LeTo37/Ukulele_Player/Mechanical_Designs/Unused_Designs/Full_Assembly.stl

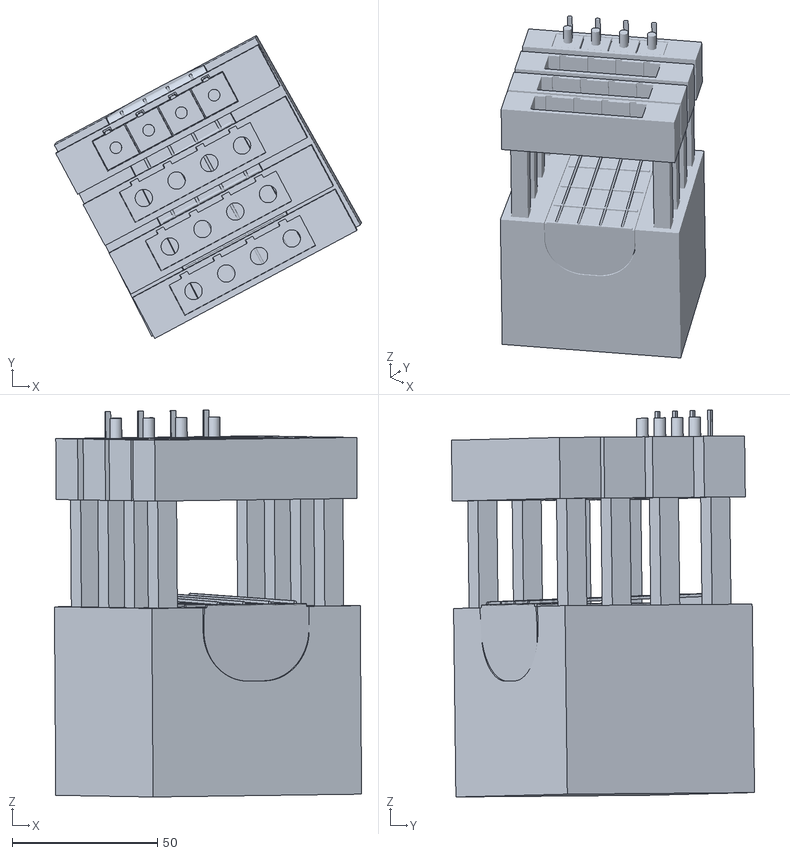
[picture p22: CAD file, 2019-02-07, an earlier design]
Mechanical_Designs/Unused_Designs/Full_Assembly.stl
105.9 x 104.5 x 133.4
