LeTo37/Ukulele_Player/Circuit_Schematics/LED.sch

## KiCad design Circuit_Schematics/LED.sch (2019-03-22)

Schematic: LED.sch

Parts:
D1: LED
D10: PIC32 Digital I/O
R1: 330
