LeTo37/Ukulele_Player/Circuit_Schematics/Solenoid_Drivers_1.sch

## KiCad design Circuit_Schematics/Solenoid_Drivers_1.sch (2019-03-22)

Schematic: Solenoid_Drivers_1.sch

Parts:
D1, D2, D3, D4, D5, D6, D7, D8: 1N4004
L1, L2, L3, L4, L5, L6, L7, L8: Solenoid
Q1, Q2, Q3, Q4, Q5, Q6, Q7, Q8: TIP120; TO-220_Vertical
R1, R2, R3, R4, R5, R6, R7, R8: 1k
RB0, RB1, RB2, RB3, RB4, RB5, RB6, RB7: PIC32 Digital I/O
