LeTo37/Ukulele_Player/Circuit_Schematics/Solenoid_Drivers_2.sch

## KiCad design Circuit_Schematics/Solenoid_Drivers_2.sch (2019-03-22)

Schematic: Solenoid_Drivers_2.sch

Parts:
D9, D10, D11, D12, D13, D14, D15, D16: 1N4004
L9, L10, L11, L12, L13, L14, L15, L16: Solenoid
Q1, Q2, Q3, Q4, Q5, Q6, Q7, Q8: TIP120; TO-220_Vertical
R9, R10, R11, R12, R13, R14, R15, R16: 1k
RB8, RB9, RB10, RB11, RB12, RB13, RB14, RB15: PIC32 Digital I/O
